VikramP7/SOAR_LaunchRailBoard/img/anemom.jpg

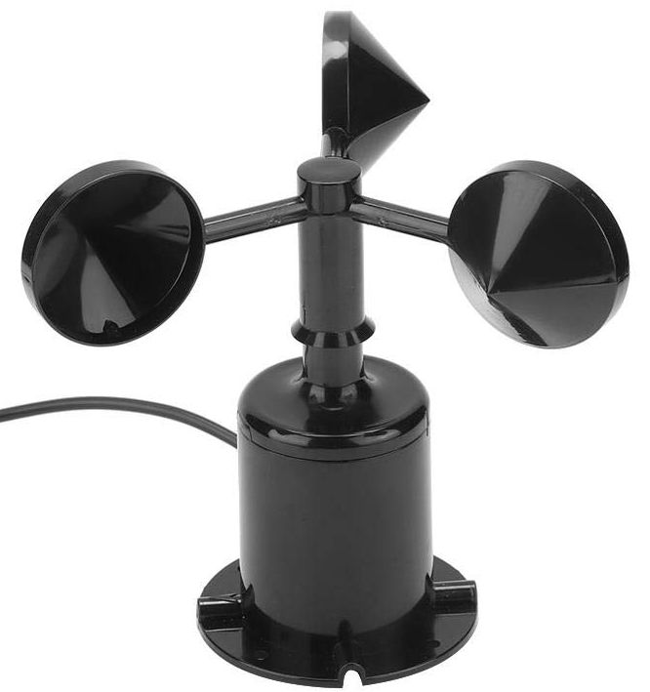
img/anemom.jpg
