VikramP7/SOAR_LaunchRailBoard/img/LRB_FSB_Circular_Connector_Standard.jpg

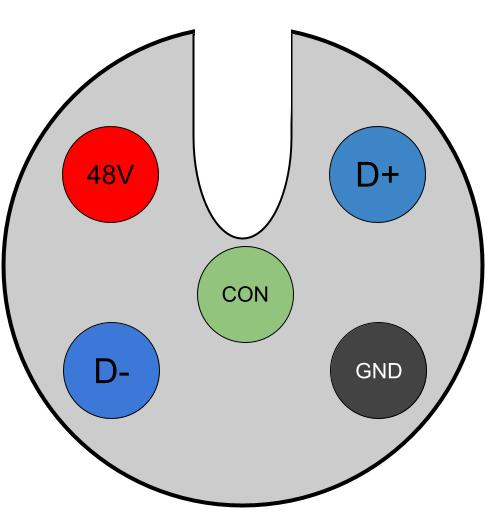
img/LRB_FSB_Circular_Connector_Standard.jpg
